abbounassima2/STM32-PLC-Runtime-Engine-and-PCB/test407.ioc

Mcu.UserName=STM32F407VETx
PA0-WKUP.Signal=ADCx_IN0
PA1.Signal=ADCx_IN1
PA10.Signal=GPIO_Output
PA12.Signal=GPIO_Output
PA13.Signal=SYS_JTMS-SWDIO
PA14.Signal=SYS_JTCK-SWCLK
PA4.Signal=COMP_DAC1_group
PA5.Signal=COMP_DAC2_group
PA8.Signal=GPIO_Output
PB14.Signal=S_TIM12_CH1
PB15.Signal=S_TIM12_CH2
PC10.Signal=UART4_TX
PC11.Signal=UART4_RX
PC12.Signal=GPIO_Output
PC2.Signal=ADCx_IN12
PC3.Signal=ADCx_IN13
PC6.Signal=GPIO_Output
PC8.Signal=GPIO_Output
PD1.Signal=GPIO_Input
PD11.Signal=GPIO_Output
PD14.Signal=GPIO_Output
PD3.Signal=GPIO_Input
PD8.Signal=USART3_TX
PD9.Signal=USART3_RX
PE10.Signal=GPIO_Input
PE11.Signal=GPIO_Input
PE12.Signal=GPIO_Input
PE13.Signal=GPIO_Input
PE8.Signal=GPIO_Input
PE9.Signal=GPIO_Input
